gvi70000/Telescope-coarse-position-system-using-BNO086-and-NEO-M9N-GNSS-module/Core/Src/i2c.c

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
/* Includes ------------------------------------------------------------------*/
#include "i2c.h"

/* USER CODE BEGIN 0 */
#include <stdio.h>
/* USER CODE END 0 */

I2C_HandleTypeDef hi2c1;

/* I2C1 init function */
void MX_I2C1_Init(void)
{

  hi2c1.Instance = I2C1;
  hi2c1.Init.Timing = 0x0000020B;
  hi2c1.Init.OwnAddress1 = 0;
  hi2c1.Init.AddressingMode = I2C_ADDRESSINGMODE_7BIT;
  hi2c1.Init.DualAddressMode = I2C_DUALADDRESS_DISABLE;
  hi2c1.Init.OwnAddress2 = 0;
  hi2c1.Init.OwnAddress2Masks = I2C_OA2_NOMASK;
  hi2c1.Init.GeneralCallMode = I2C_GENERALCALL_DISABLE;
  hi2c1.Init.NoStretchMode = I2C_NOSTRETCH_DISABLE;
  if (HAL_I2C_Init(&hi2c1) != HAL_OK)
  {
    Error_Handler();
  }

  /** Configure Analogue filter
  */
  if (HAL_I2CEx_ConfigAnalogFilter(&hi2c1, I2C_ANALOGFILTER_ENABLE) != HAL_OK)
  {
    Error_Handler();
  }

  /** Configure Digital filter
  */
  if (HAL_I2CEx_ConfigDigitalFilter(&hi2c1, 0) != HAL_OK)
  {
    Error_Handler();
  }
}

void HAL_I2C_MspInit(I2C_HandleTypeDef* i2cHandle)
{

  GPIO_InitTypeDef GPIO_InitStruct = {0};
  if(i2cHandle->Instance==I2C1)
  {
    __HAL_RCC_GPIOB_CLK_ENABLE();
    /**I2C1 GPIO Configuration
    PB8     ------> I2C1_SCL
    PB9     ------> I2C1_SDA
    */
    GPIO_InitStruct.Pin = GPIO_PIN_8|GPIO_PIN_9;
    GPIO_InitStruct.Mode = GPIO_MODE_AF_OD;
    GPIO_InitStruct.Pull = GPIO_NOPULL;
    GPIO_InitStruct.Speed = GPIO_SPEED_FREQ_HIGH;
    GPIO_InitStruct.Alternate = GPIO_AF4_I2C1;
    HAL_GPIO_Init(GPIOB, &GPIO_InitStruct);

    /* I2C1 clock enable */
    __HAL_RCC_I2C1_CLK_ENABLE();
  }
}

void HAL_I2C_MspDeInit(I2C_HandleTypeDef* i2cHandle)
{

  if(i2cHandle->Instance==I2C1)
  {
    /* Peripheral clock disable */
    __HAL_RCC_I2C1_CLK_DISABLE();

    /**I2C1 GPIO Configuration
    PB8     ------> I2C1_SCL
    PB9     ------> I2C1_SDA
    */
    HAL_GPIO_DeInit(GPIOB, GPIO_PIN_8);

    HAL_GPIO_DeInit(GPIOB, GPIO_PIN_9);

  }
}

/* USER CODE BEGIN 1 */
void myI2C_Scan(void) {
	//printf("Scanning I2C bus...\r\n");
	HAL_StatusTypeDef res;
	for(uint16_t i = 0; i < 128; i++) {
		uint8_t j = (i << 1);
		res = HAL_I2C_IsDeviceReady(&hi2c1, j, 1, 10);
			if(res == HAL_OK) {
				printf("Found devive at 0x%X (0x%X)\r\n", j, i); // Received an ACK at that address
			}
	}
}
/* USER CODE END 1 */
